boriz/MetalDetector/MetalDetector.asc

C1: cap; 100nF
D1: schottky; 1N5817
L1: ind; 1mH
R2: res; 100K
R3: res; 470
V1: voltage; PULSE(0 5 0 1ns 1ns 10us 20us 300)
Named nets: 0, P9_GEN, A0_FB
.tran 5ms
